cotrin8672/ReeL/model/reel_right_top_neo2.step

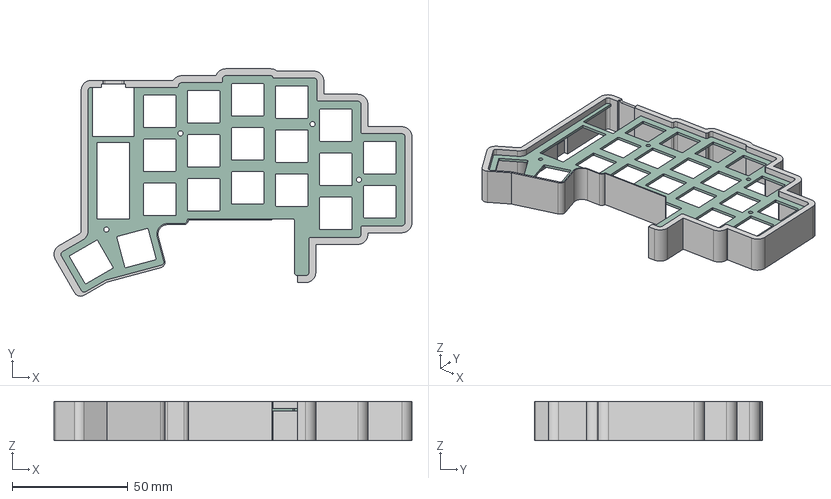
[picture p12: CAD file, 2026-08-24]
model/reel_right_top_neo2.step
154.5 x 98.2 x 17.0 mm
