cotrin8672/ReeL/model/reel_right_bottom.step

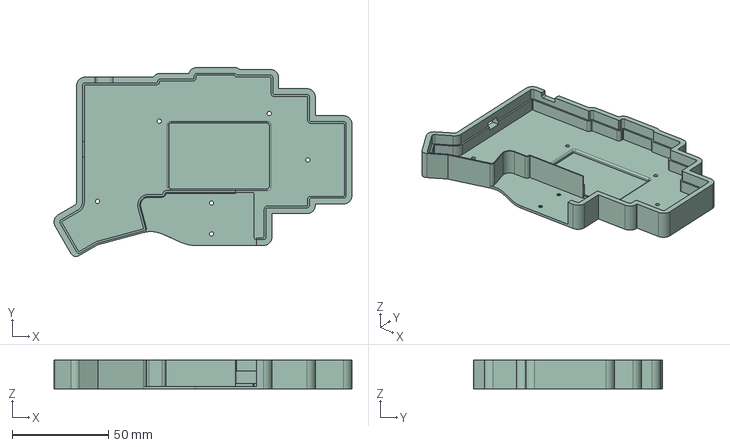
[picture p13: CAD file, 2026-08-18]
model/reel_right_bottom.step
154.5 x 98.0 x 15.0 mm
