cotrin8672/ReeL/model/encoder_shaft.step

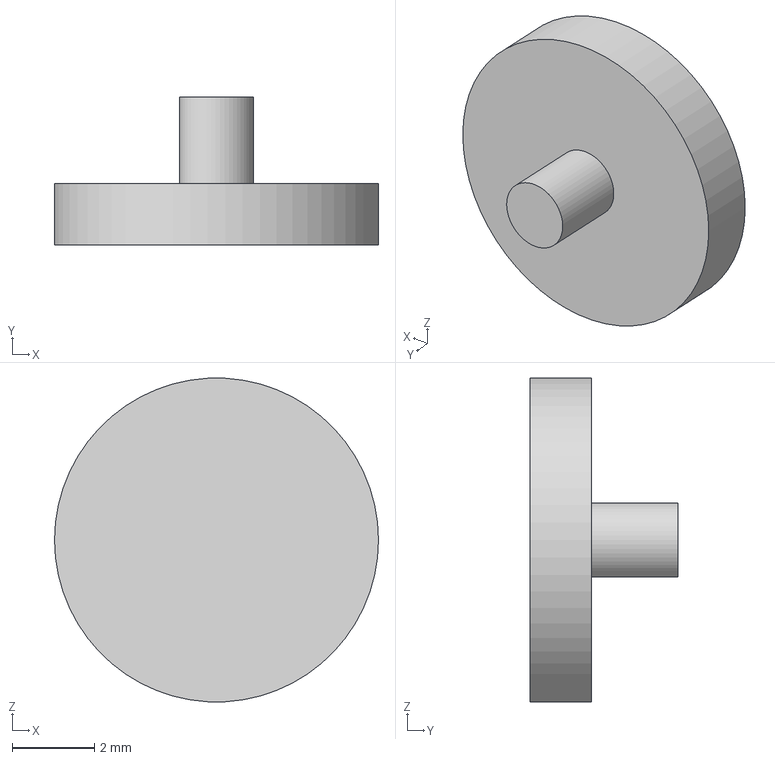
[picture p14: CAD file, 2026-08-16]
model/encoder_shaft.step
7.90 x 3.60 x 7.89 mm
