cotrin8672/ReeL/model/reel_left_bottom.step

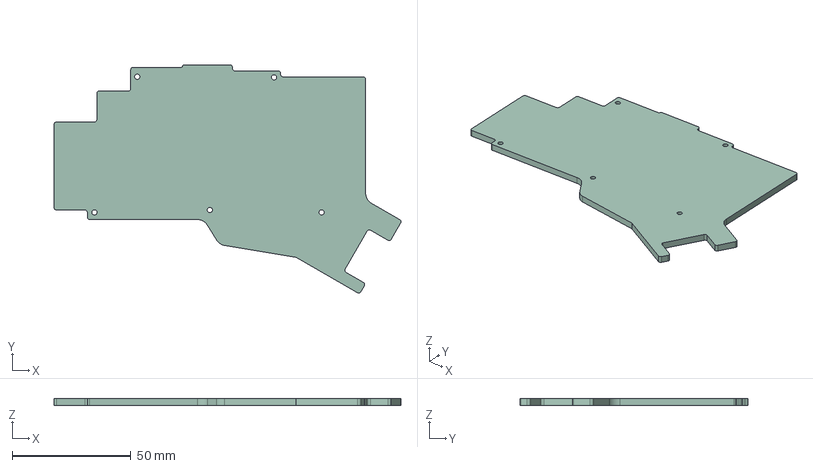
[picture p15: CAD file, 2026-07-30]
model/reel_left_bottom.step
145.9 x 95.9 x 2.80 mm
