cotrin8672/ReeL/model/reel_left_top.step

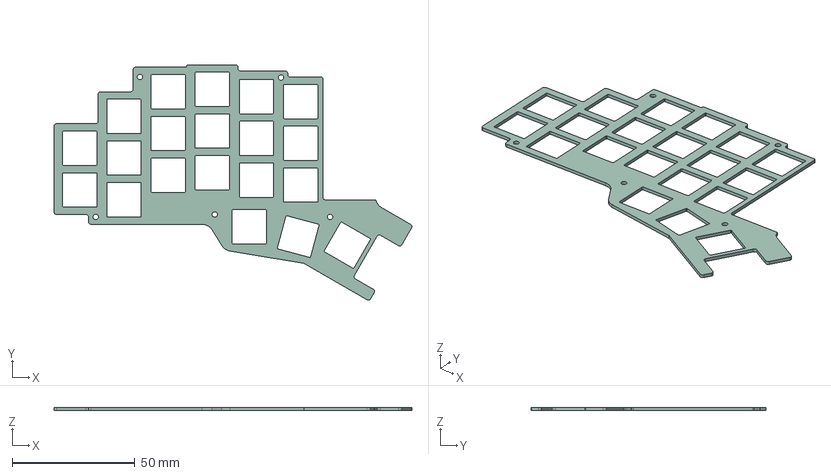
[picture p16: CAD file, 2026-07-30]
model/reel_left_top.step
145.9 x 95.9 x 1.20 mm
