cotrin8672/ReeL/model/RotaryEncoderTest.stl

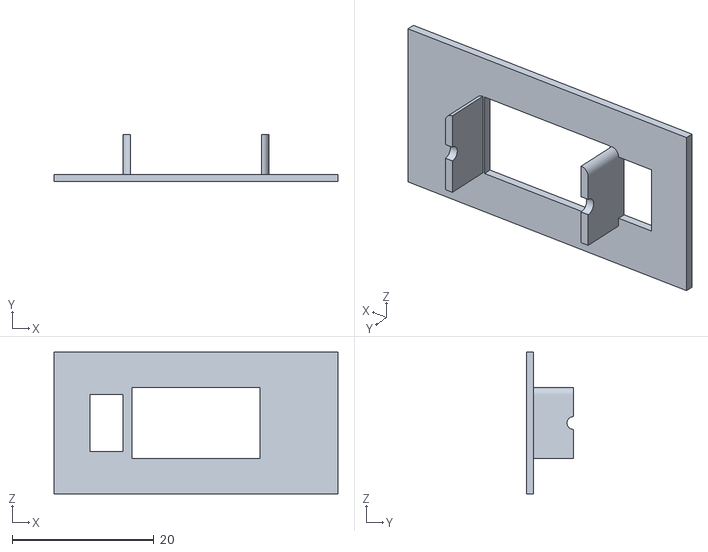
[picture p17: CAD file, 2026-07-15]
model/RotaryEncoderTest.stl
40.0 x 6.60 x 20.0
