cotrin8672/ReeL/model/TrackballCase.stl

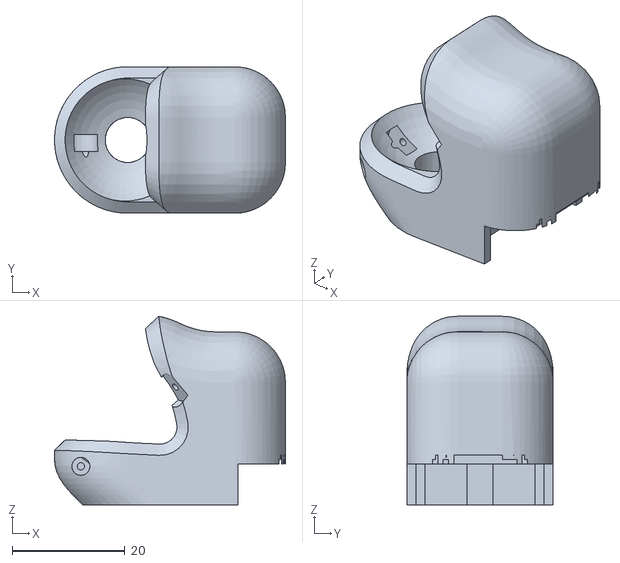
[picture p18: CAD file, 2026-07-11]
model/TrackballCase.stl
41.0 x 26.0 x 33.5
